willfoerster/Group_Name_Project/PCB/Laser Module.png

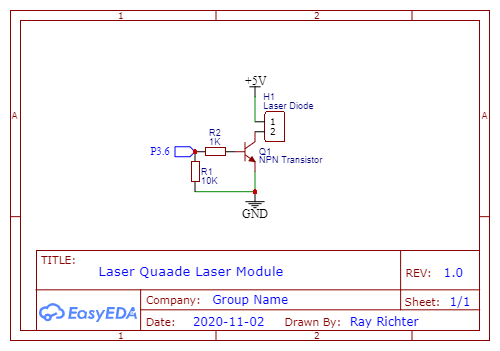
PCB/Laser Module.png
