willfoerster/Group_Name_Project/PCB/PCB_PCB_2020-12-05_22-15-21_2020-12-05_22-37-24.png

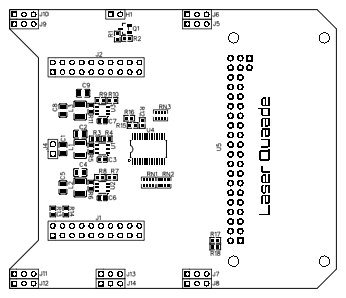
PCB/PCB_PCB_2020-12-05_22-15-21_2020-12-05_22-37-24.png
