willfoerster/Group_Name_Project/PCB/Power.png

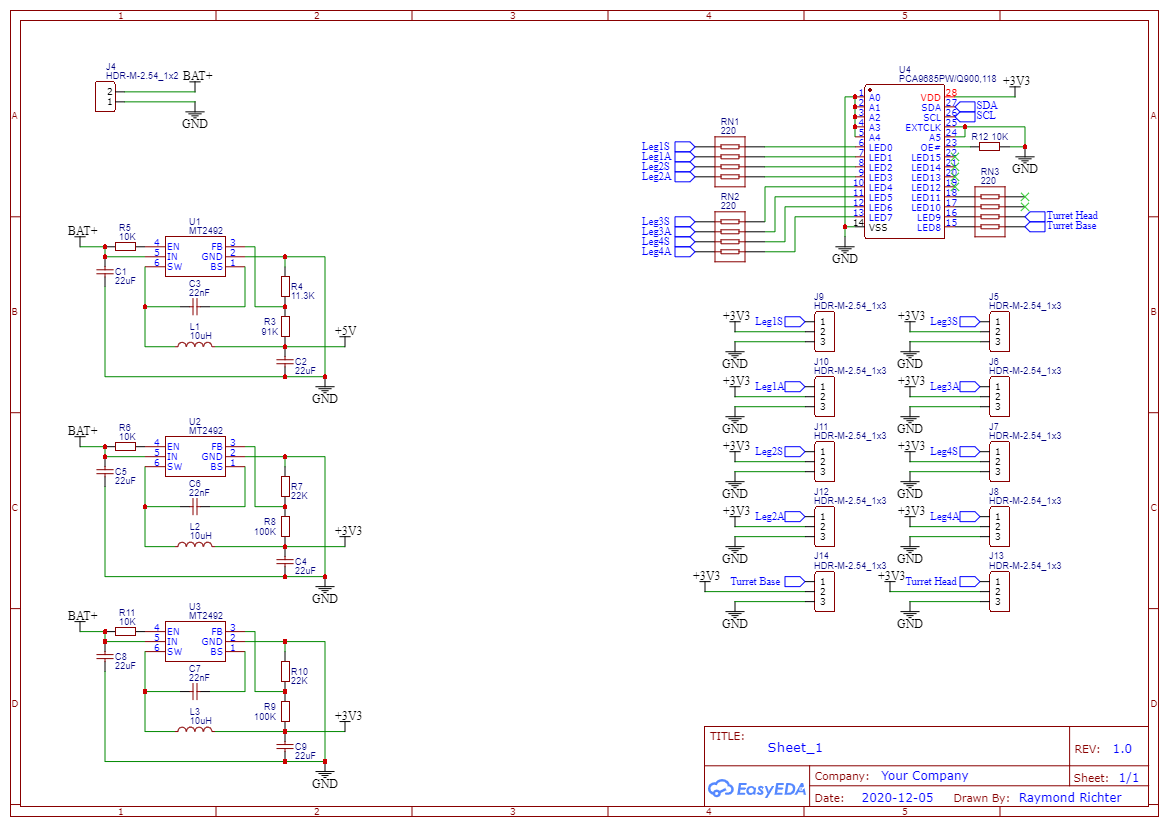
PCB/Power.png
