willfoerster/Group_Name_Project/PCB/RasPi Z W.png

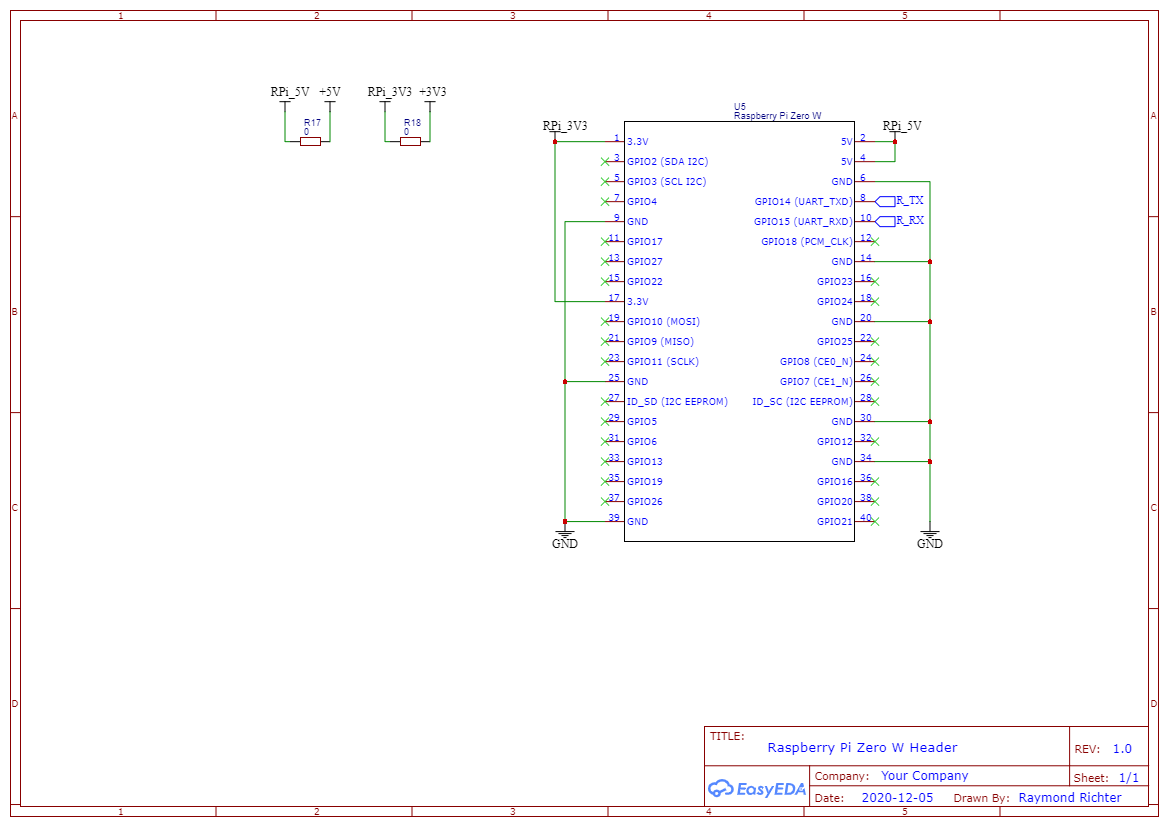
PCB/RasPi Z W.png
