willfoerster/Group_Name_Project/Quaade_movement/servo.h

/*
 * servo.h
 *
 *  Created on: Jul 14, 2020
 *      Author: Tyler Davidson
 */

#ifndef SERVO_H_
#define SERVO_H_

#include "pca9685.h"

//Servo Definitions
//-----Servo-----Channel
#define URL         0
#define LRL         1

#define URA         4
#define LRA         5

#define VCT         6 //vertical central turret
#define HCT         7 //horizontal central turret

#define ULL         9
#define LLL         10

#define ULA         13
#define LLA         14

//URA-> Upper Right Arm
//LLL-> Lower Left Leg
//etc.


#endif /* SERVO_H_ */
